Leoneq/iNapMalinka/docs/pics/full_malina_white.png

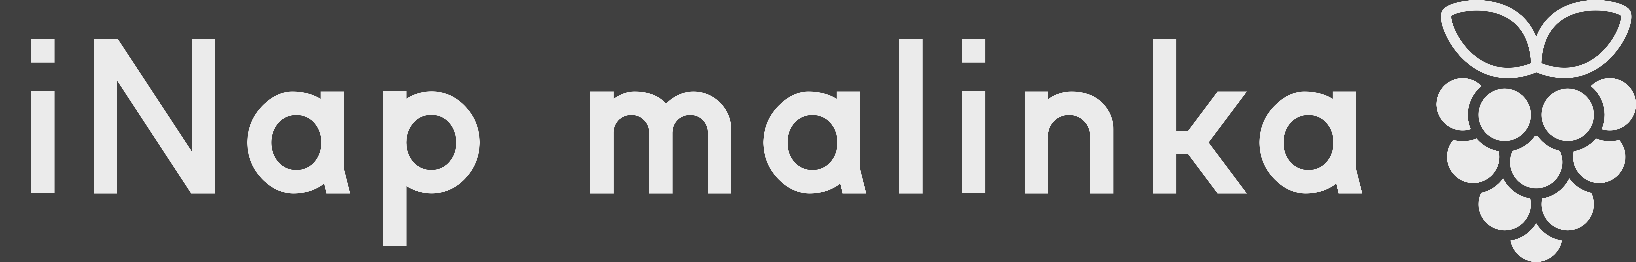
docs/pics/full_malina_white.png
