Leoneq/iNapMalinka/docs/pics/layout.png

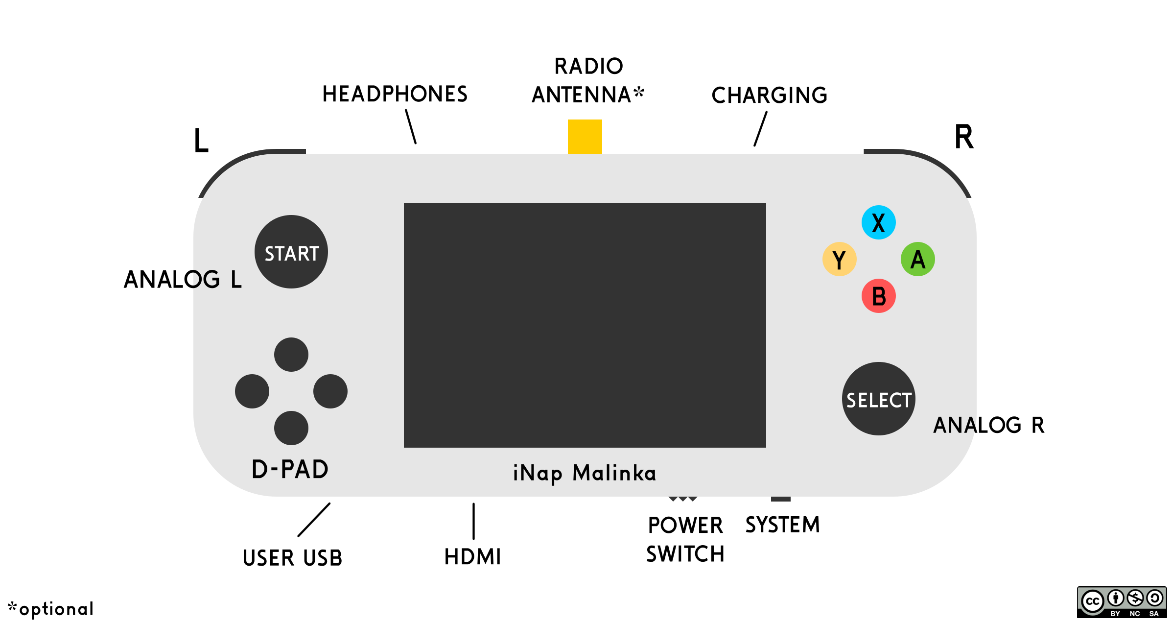
docs/pics/layout.png
